kimmoli/tohkbd-archive/daemon/src/tohkbd.cpp

/*
 * (C) 2014 Kimmo Lindholm <kimmo.lindholm@gmail.com> Kimmoli
 *
 * Main, Daemon functions
 *
 */

#include <stdio.h>
#include <fcntl.h>
#include <signal.h>
#include <unistd.h>
#include <sys/stat.h>
#include <sys/types.h>
#include "tohkeyboard.h"
#include "toh.h"

#include <QtCore/QCoreApplication>
#include <QDBusConnection>

static void daemonize();
static void signalHandler(int sig);


int main(int argc, char **argv)
{
    QCoreApplication app(argc, argv);

    daemonize();

    setlinebuf(stdout);
    setlinebuf(stderr);

    printf("Starting tohkbd daemon. V%s build %s %s\n", VERSION_NUMBER,  __DATE__, __TIME__);

    QDBusConnection mceSignalconn = QDBusConnection::systemBus();
    if (!mceSignalconn.isConnected())
    {
        printf("Cannot connect to the D-Bus systemBus\n%s\n",
               qPrintable(mceSignalconn.lastError().message()));
        sleep(3);
        exit(EXIT_FAILURE);
    }
    printf("Connected to D-Bus systembus\n");

    Tohkbd tohkbd;

    /* Nokia MCE display_status_ind
     * used to enable and disable keyboard when display is on or off
     */
    mceSignalconn.connect("com.nokia.mce", "/com/nokia/mce/signal", "com.nokia.mce.signal", "display_status_ind",
                          &tohkbd, SLOT(handleDisplayStatus(const QDBusMessage&)));
    return app.exec();
}

static void daemonize()
{
    /* Change the file mode mask */
    umask(0);

    /* Change the current working directory */
    if ((chdir("/tmp")) < 0)
        exit(EXIT_FAILURE);

    /* register signals to monitor / ignore */
    signal(SIGCHLD,SIG_IGN); /* ignore child */
    signal(SIGTSTP,SIG_IGN); /* ignore tty signals */
    signal(SIGTTOU,SIG_IGN);
    signal(SIGTTIN,SIG_IGN);
    signal(SIGHUP,signalHandler); /* catch hangup signal */
    signal(SIGTERM,signalHandler); /* catch kill signal */
}


static void signalHandler(int sig) /* signal handler function */
{
    switch(sig)
    {
        case SIGHUP:
            /* rehash the server */
            printf("Received signal SIGHUP\n");
            break;
        case SIGTERM:
            /* finalize the server */
            printf("Received signal SIGTERM\n");
            controlVdd(0);
            exit(0);
            break;
    }
}
